CircuitCraftsman/USB-to-SATA-bridge/USB to SATA bridge/Simulation/Results/1726425964811.jpeg

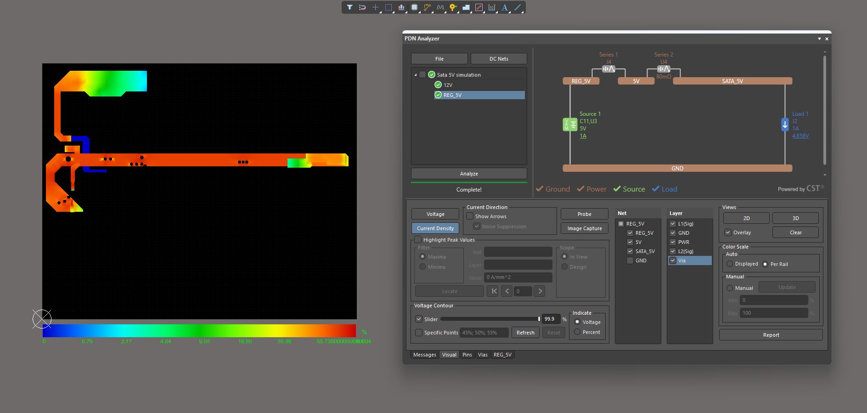
USB to SATA bridge/Simulation/Results/1726425964811.jpeg
